Plajta/Sisyphus/PCBs/rgb_sensor/rgb_sensor_3d/VEML3328/80216oplga4l.stp

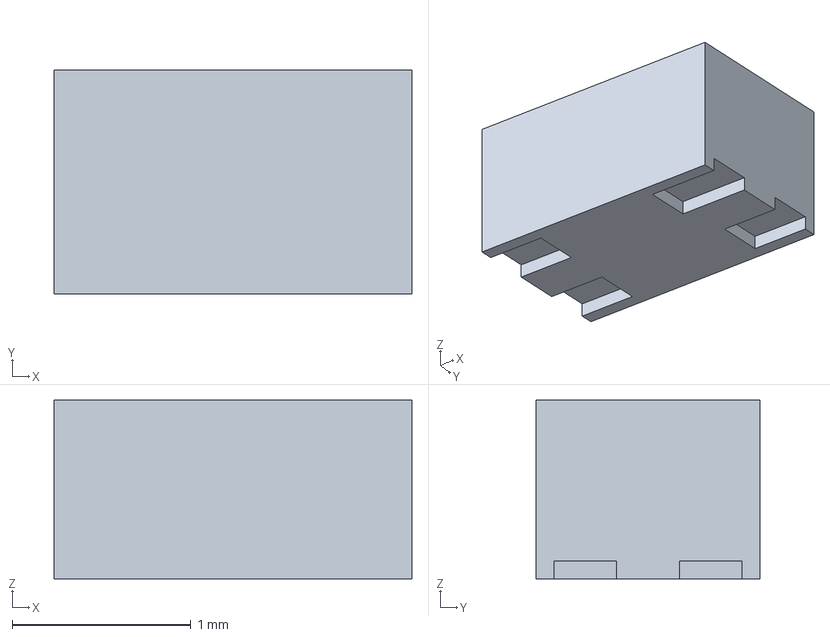
[picture p15: CAD file, 2025-06-02]
PCBs/rgb_sensor/rgb_sensor_3d/VEML3328/80216oplga4l.stp
2.00 x 1.25 x 1.00 mm
