Plajta/Sisyphus/src/battery/charger/bq25619/bq25619.h

#pragma once
#include <hardware/i2c.h>

#define VBUS_STATUS_NONE 0
#define VBUS_STATUS_USB_HOST 1
#define VBUS_STATUS_ADAPTER 3
#define VBUS_STATUS_BOOST_MODE 7

#define CHARGING_STATUS_NOT_CHARGING 0
#define CHARGING_STATUS_PRECHARGING_TRICKLE 1
#define CHARGING_STATUS_FAST_CHARGING 2
#define CHARGING_STATUS_TERMINATED 3

#define CHARGING_FAULT_NONE 0
#define CHARGING_FAULT_INPUT 1
#define CHARGING_FAULT_TEMPERATURE 2
#define CHARGING_FAULT_TIMEOUT 3

#define NTC_TEMP_NORMAL 0
#define NTC_TEMP_WARM 2
#define NTC_TEMP_COOL 3
#define NTC_TEMP_COLD 5
#define NTC_TEMP_HOT 6

#define BQ25619_DEFAULT_CHARGE_CURRENT_LIMIT SISYFOSS_PMIC_MAX_CHARGE_CURRENT
#define BQ25619_DEFAULT_INPUT_CURRENT_LIMIT SISYFOSS_PMIC_MAX_INPUT_CURRENT
#define BQ25619_DEFAULT_CHARGE_VOLTAGE_LIMIT SISYFOSS_PMIC_MAX_CHARGE_VOLTAGE
#define BQ25619_DEFAULT_PRECHARGE_CURRENT_LIMIT SISYFOSS_PMIC_MAX_PRECHARGE_CURRENT
#define BQ25619_DEFAULT_TERMINATION_CURRENT_LIMIT SISYFOSS_PMIC_MAX_TERMINATION_CURRENT

typedef union {
    struct {
        // STATUS_2 register
        bool cin_dpm_irq          : 1; // Bit 0
        bool vin_dpm_irq          : 1; // Bit 1
        bool acov_mode            : 1; // Bit 2
        bool in_topoff            : 1; // Bit 3
        bool bat_sense_ok         : 1; // Bit 4
        bool cin_dpm_mode         : 1; // Bit 5 // Input dynamic current management
        bool vin_dpm_mode         : 1; // Bit 6 // Input dynamic voltage management
        bool vbus_source_good     : 1; // Bit 7

        // STATUS_0 register
        bool sys_regulation       : 1; // Bit 0
        bool termal_regulated     : 1; // Bit 1
        bool power_good           : 1; // Bit 2
        uint8_t charge_status     : 2; // Bits 3-4
        uint8_t vbus_status       : 3; // Bits 5-7
    };
    struct {
        uint8_t raw_status2;
        uint8_t raw_status0;
    };
    uint16_t raw_all;
} bq25619_status;

typedef union {
    struct {
        uint8_t ntc_temp           : 3; // Bits 0-2
        bool battery_overvoltage   : 1; // Bit 3
        uint8_t charge_fault       : 2; // Bits 4-5
        bool boost_fault           : 1; // Bit 6
        bool watchdog_expired      : 1; // Bit 7
    };
    uint8_t raw_status1;
} bq25619_fault_status;

int bq25619_init(i2c_inst_t *i2c);
int bq25619_read_status(i2c_inst_t *i2c, bq25619_status *status);
int bq25619_read_fault_status(i2c_inst_t *i2c, bq25619_fault_status *fault_status);
